Simv135/Rivellino-Smart-Sensors/schemi_elettrici/modulo_A/KiCAD/ModuloA.kicad_sch

## KiCad design schemi_elettrici/modulo_A/KiCAD/ModuloA.kicad_sch (2025-11-30)

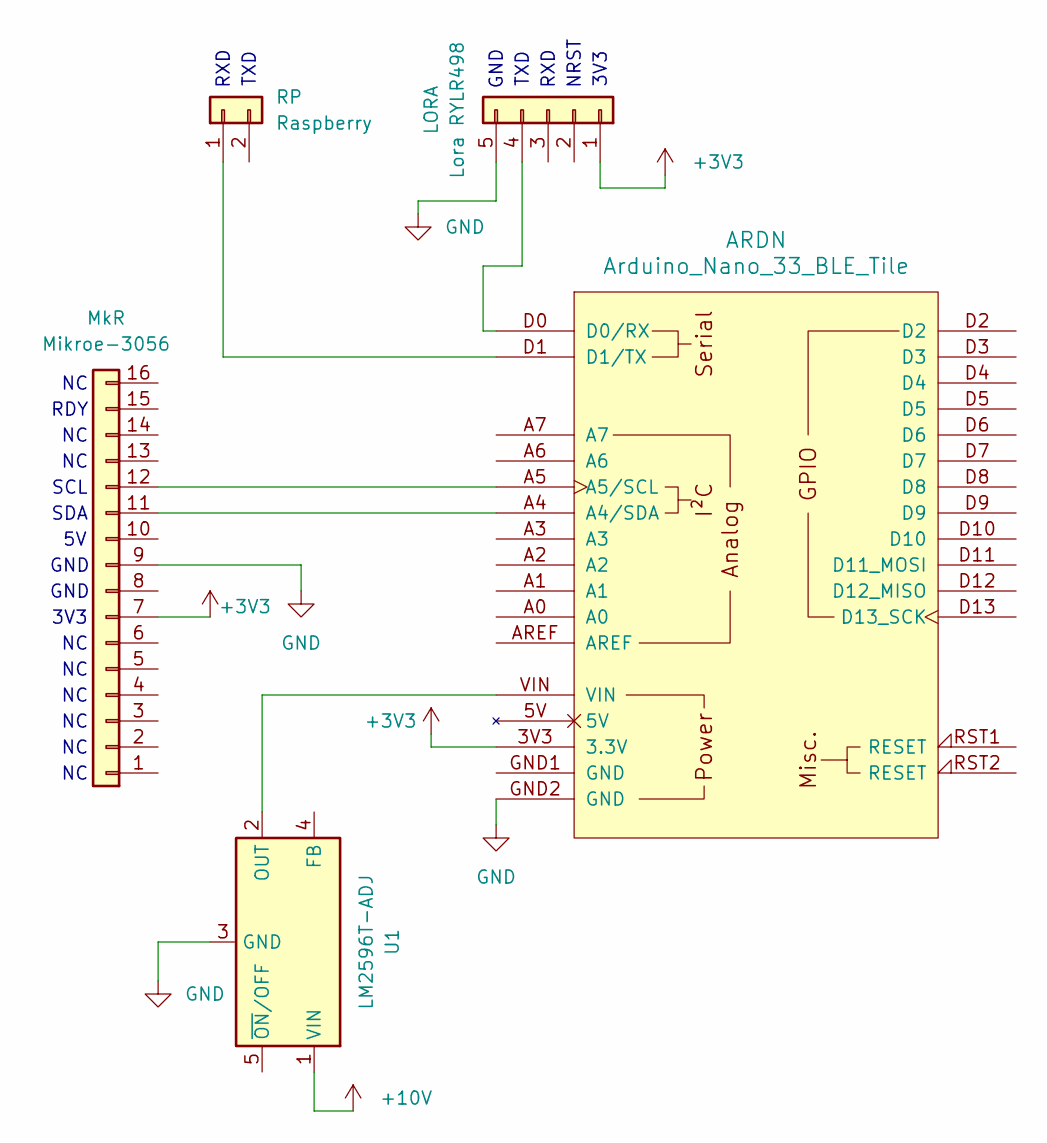
[picture p14: schematic ModuloA.kicad_sch]

Parts:
ARDN: Arduino_Nano_33_BLE_Tile; Arduino_Nano_Every_Tile
LORA: Lora RYLR498
MkR: Mikroe-3056
RP: Raspberry
U1: LM2596T-ADJ; TO-220-5_P3.4x3.7mm_StaggerOdd_Lead3.8mm_Vertical

Connections:
+3V3: ARDN.3V3 (3.3V), LORA.1, MkR.7
+10V: U1.1 (VIN)
GND: ARDN.GND2 (GND), LORA.5, MkR.9, U1.3 (GND)
unnamed: ARDN.A4 (A4/SDA), MkR.11
unnamed: ARDN.A5 (A5/SCL), MkR.12
unnamed: ARDN.D0 (D0/RX), LORA.4
unnamed: ARDN.D1 (D1/TX), RP.1
unnamed: ARDN.VIN, U1.2 (OUT)

Notes on the sheet:
RXD
GND
NRST
3V3
RDY
SCL
SDA
TXD
