Simv135/Rivellino-Smart-Sensors/schemi_elettrici/modulo_B/KiCAD/ModuloB.kicad_sch

## KiCad design schemi_elettrici/modulo_B/KiCAD/ModuloB.kicad_sch (2025-11-30)

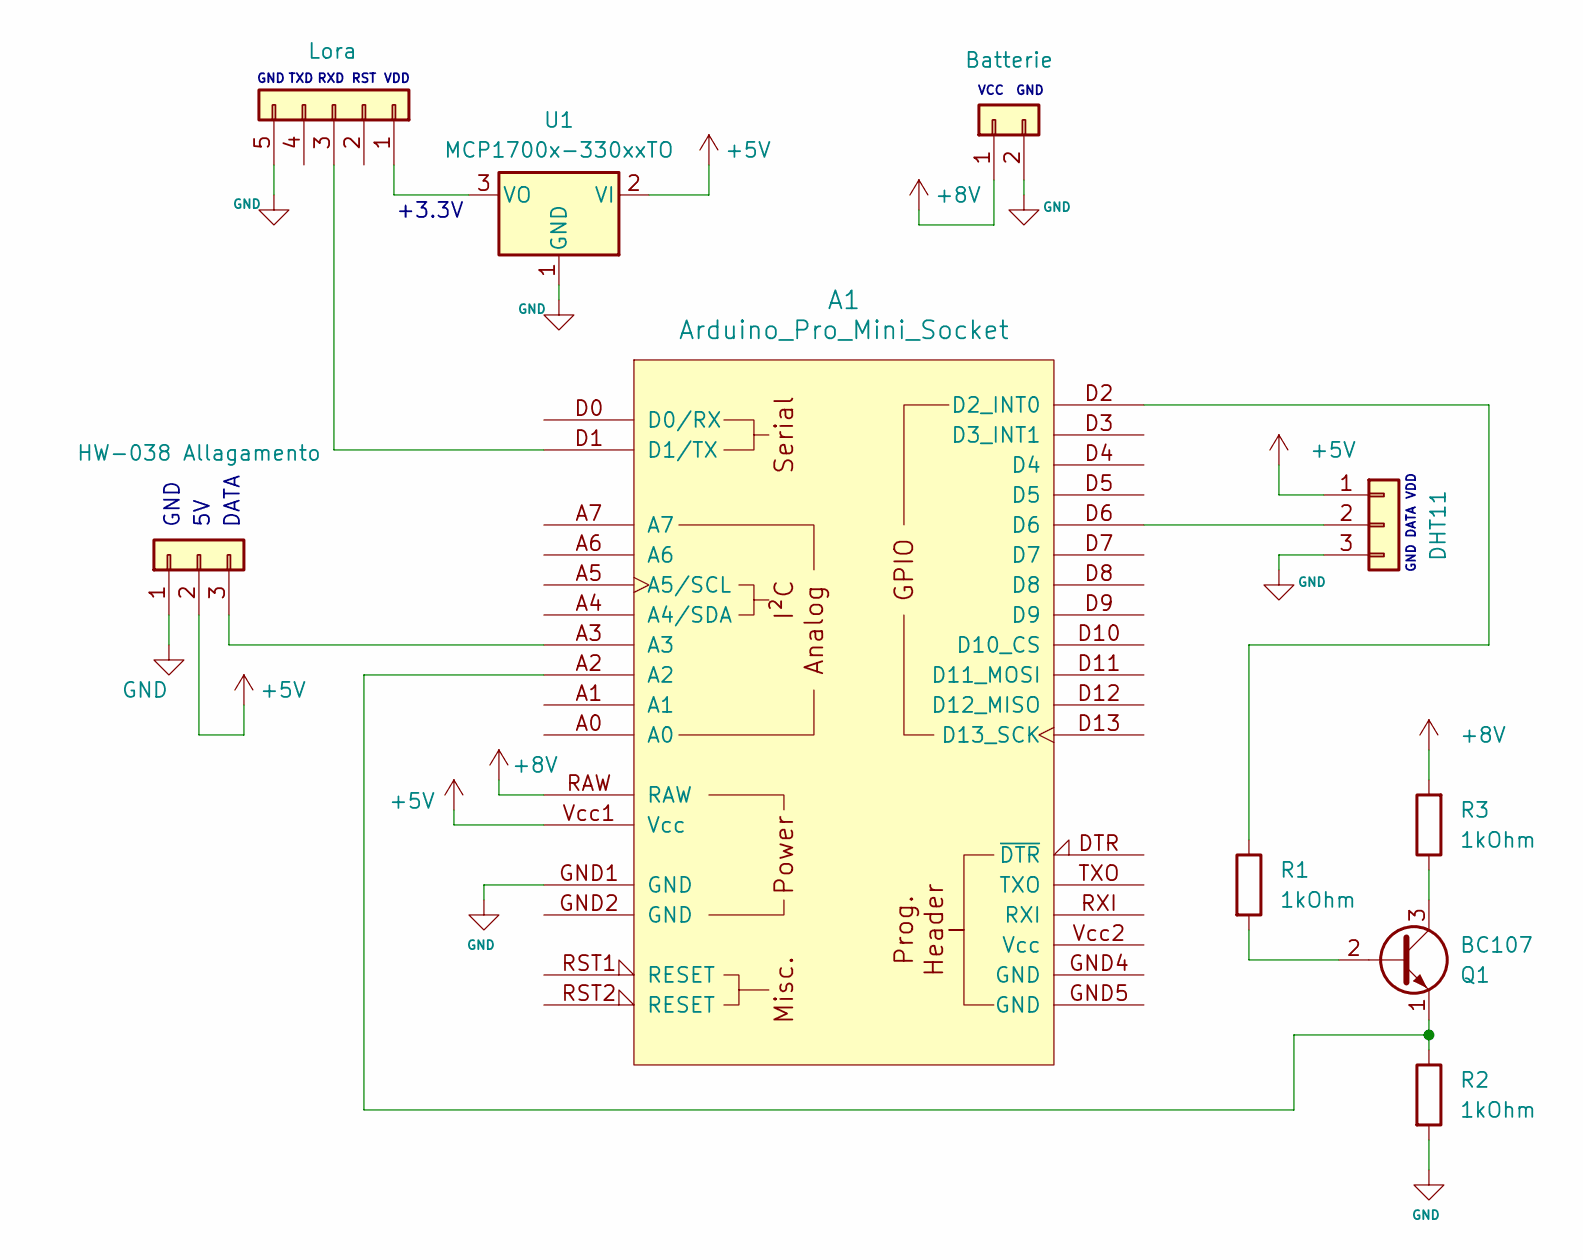
[picture p15: schematic ModuloB.kicad_sch]

Parts:
A1: Arduino_Pro_Mini_Socket
Batterie: Conn_01x02
DHT11: Conn_01x03
HW-38: HW-038 Allagamento
Lora: Conn_01x05
Q1: BC107; TO-18-3
R1, R2, R3: 1kOhm
U1: MCP1700x-330xxTO; TO-92_Inline

Connections:
+5V: A1.Vcc1 (Vcc), DHT11.1, HW-38.2, U1.2 (VI)
+8V: A1.RAW, Batterie.1, R3.2
GND: A1.GND1 (GND), Batterie.2, DHT11.3, HW-38.1, Lora.5, R2.2, U1.1 (GND)
unnamed: A1.A2, Q1.1 (E), R2.1
unnamed: A1.A3, HW-38.3
unnamed: A1.D1 (D1/TX), Lora.3
unnamed: A1.D2 (D2_INT0), R1.1
unnamed: A1.D6, DHT11.2
unnamed: Lora.1, U1.3 (VO)
unnamed: Q1.2 (B), R1.2
unnamed: Q1.3 (C), R3.1

Notes on the sheet:
VCC
GND
DATA
TXD
GND
VDD
+3.3V
RXD
RST
VDD
